doducminh/3d-models-aquarium-cory-shrimp-shelter/gcode/doc-kinh-truoc/than-hang.png

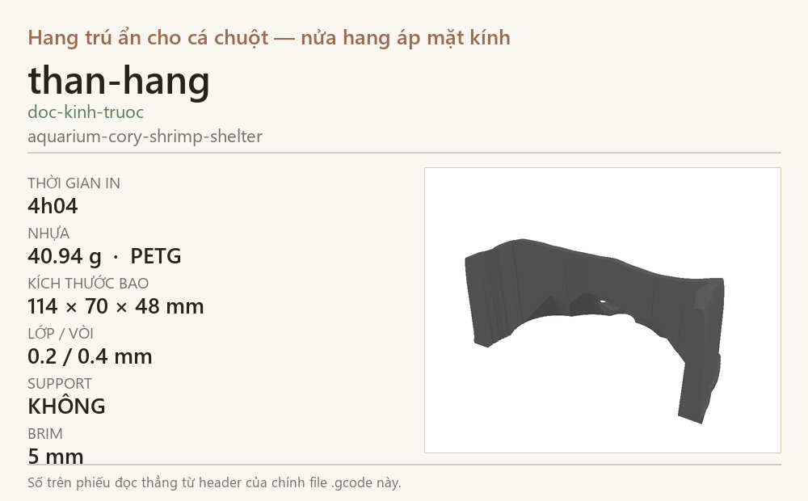
gcode/doc-kinh-truoc/than-hang.png
